Alireza255/solar_sense_node/resources/boxes/h102.pdf

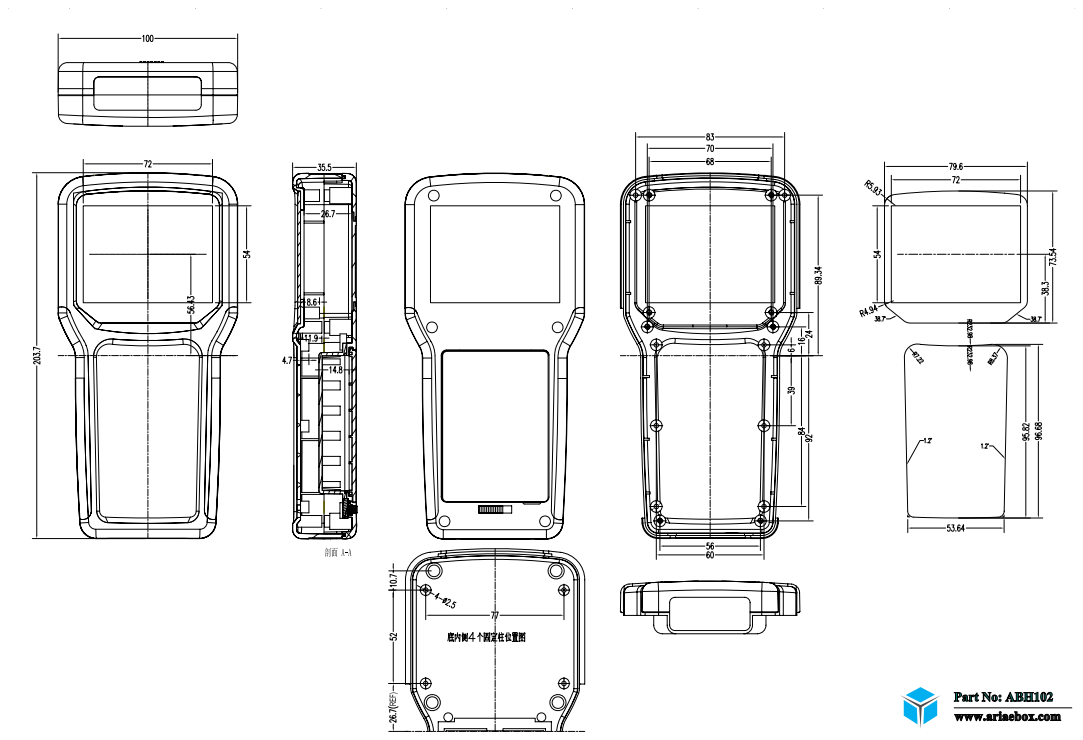
[picture p18: page 1]

Part No: ABH102
www.ariaebox.com
