Alireza255/solar_sense_node/resources/boxes/h105.pdf

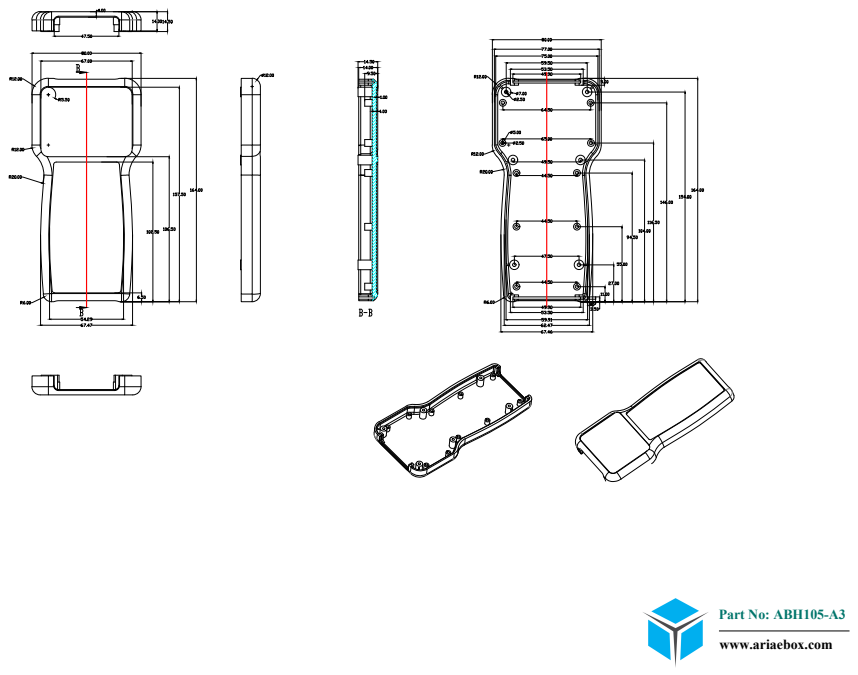
[picture p19: page 1]
Part No: ABH105-A3

www.ariaebox.com

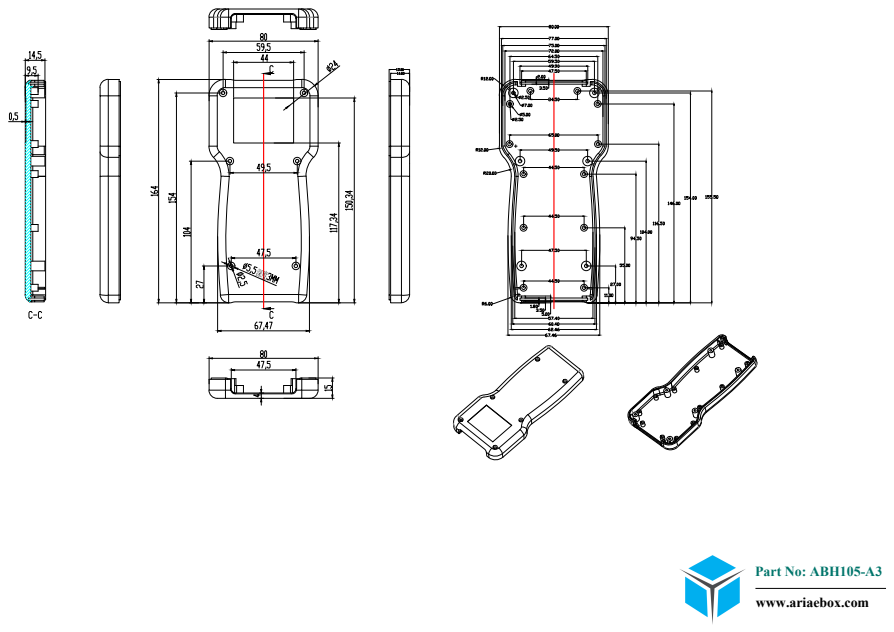
[picture p20: page 2]
Part No: ABH105-A3

www.ariaebox.com

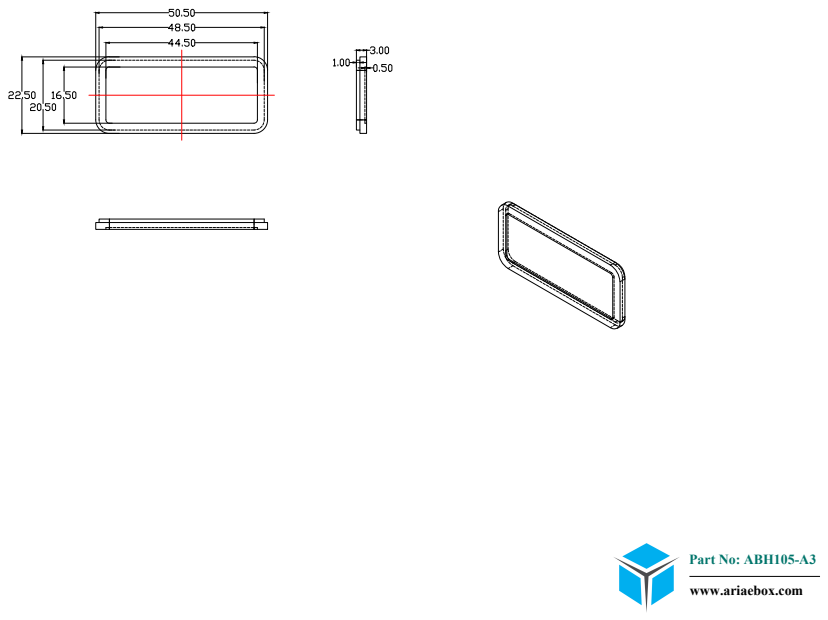
[picture p21: page 3]
Part No: ABH105-A3

www.ariaebox.com
