Alireza255/solar_sense_node/resources/boxes/h120.pdf

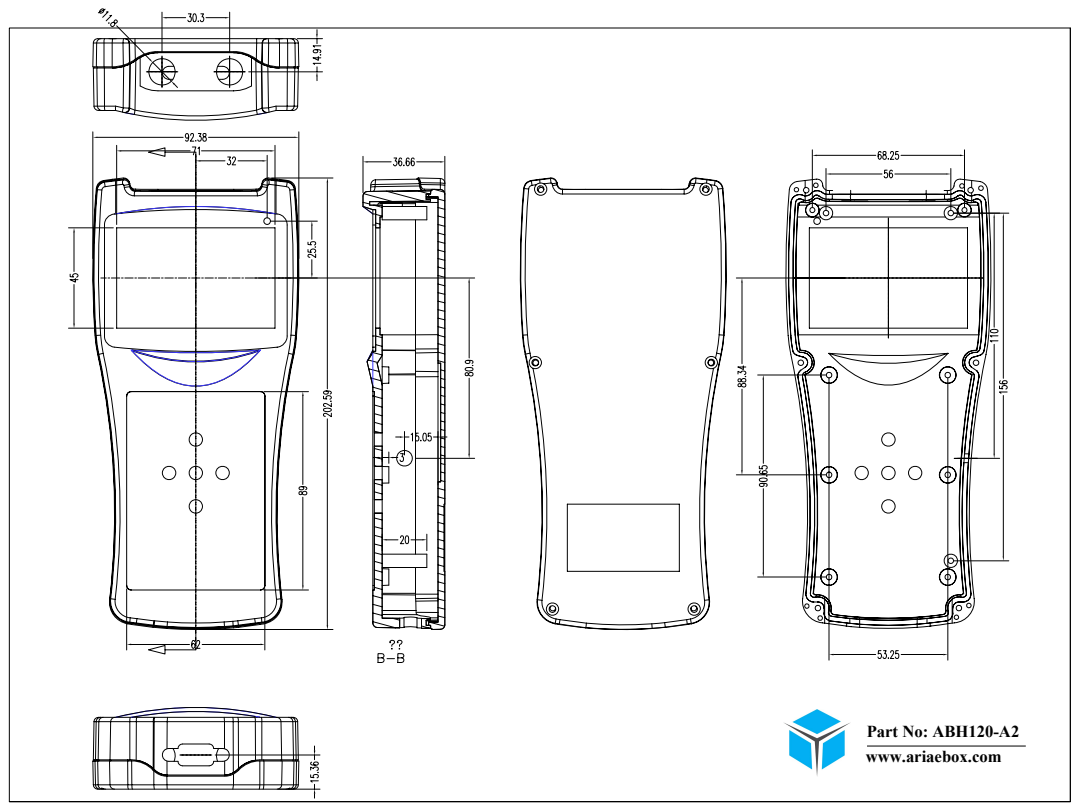
[picture p22: page 1]

Part No: ABH120-A2
www.ariaebox.com
